BotaAndreiD/Licenta/SimulariLtspice/BlackBox/Electrozi.asc

50HZ: voltage; SINE(0 100m 50)
BaseLineWander: voltage; SINE(0 1 0.02)
CmodelLA: cap; {Cla}
CmodelRA: cap; {Cra}
E1: e; 0.5
E2: e; -0.5
E3: e; -1
EMG: voltage; SINE(0 100m 200)
RmodelLA: res; {Rla}
RmodeRA: res; {Rra}
V1: voltage; PWL file=C:\Users\botaa\Documents\Licenta\AchizitionareSemnal\ekg_signal2.txt
Named nets: 0, VCM, Potential_Corp, LA, RA, RL
