BotaAndreiD/Licenta/SimulariLtspice/BlackBox/Protectie.asc

D1: zener; DI_BZX84C3V6
D2: zener; DI_BZX84C3V6
D3: zener; DI_BZX84C3V6
D4: zener; DI_BZX84C3V6
D5: diode; SMBJ90CA
D6: diode; SMBJ90CA
R1: res; 20k
R2: res; 20k
R3: res; 10k
R4: res; 10k
Named nets: 0, Vcc, ProtectieOut+, ProtectieOut-, ProtectieIn+, ProtectieIn-
.SUBCKT SMBJ90CA     1   2
*       TERMINALS:   T1  T2
Done    1            3   Dtvs
Dtwo    2            3   Dtvs
Rleak   1            2   180meg
.MODEL  Dtvs         D   (IS=1.0e-7 RS=0.4561 N=1.5 IBV=1m BV=105.5 CJO=180p)
.ENDS
