BotaAndreiD/Licenta/SimulariLtspice/BlackBox/PSU.asc

C2: cap; 1u
C3: cap; 1u; Rser=0.5
D1: zener; DI_BZX84C3V6
R1: res; 100k
R2: res; 100k
U1: ADP151-3.3
U2: opamp2; ad8534
Vusb1: voltage; 5
Named nets: 0, Vref, Vcc
