BotaAndreiD/Licenta/SimulariLtspice/BlackBox/RLD.asc

C1: cap; 1n
R7: res; 10Meg
R8: res; 1Meg
U1: opamp2; ad8534
Named nets: Vref, RL, Vcc, 0, VMED
