BotaAndreiD/Licenta/SimulariLtspice/BlackBox/SistemAchizitieECG.asc

R1: res; 10Meg
R2: res; 10Meg
X1: INA
X2: RLD
X3: Electrozi; Rla=51k Rra=100k Cla=47n Cra=47n
X4: FTS
X5: Protectie
X6: FTJ
X7: PSU
X8: NOTCH50
Named nets: VFTJ, Vref, Vcc, VINA, VFTS, VNOTCH
.lib ad8534.cir
.tran 0 35 30
.inc BZX84C3V6.spice.txt
Param. Electrozi
