BotaAndreiD/Licenta/SimulariLtspice/Standard IEC 60601-2-25/EkgIdealFinal.asc

C1: cap; 1000p
C2: cap; 0.1µ
C3: cap; 1µ; Rser=0.5
C4: cap; 1µ
C5: cap; 1µ
C6: cap; 47n
C7: cap; 10µ
C8: cap; 10µ
C9: cap; 10µ
C10: cap; 0.1µ
C11: cap; 0.1µ
C12: cap; 0.22µ
C13: cap; 4700p
C14: cap; 0.1µ
C15: cap; 0.1µ
C16: cap; 47n
C17: cap; 0.1µ
D1: zener; DI_BZX84C3V3
D2: zener; DI_BZX84C3V3
D3: zener; DI_BZX84C3V3
D4: zener; DI_BZX84C3V3
D5: diode; SMBJ90CA
D6: diode; SMBJ90CA
E1: e; 0.5
E2: e; -0.5
E3: e; -1
R1: res; 3Meg
R2: res; 3Meg
R3: res; 1Meg
R4: res; 10Meg
R5: res; 8.66k
R6: res; 100k
R7: res; 100k
R8: res; 316k
R9: res; 20k
R10: res; 158k
R11: res; 620k
R12: res; 1k
R13: res; 10k
R14: res; 31.6k
R15: res; 31.6k
R16: res; 15.4k
R17: res; 274k
R18: res; 3.01k
R19: res; 6.81k
R20: res; 3.92k
R21: res; 23.7k
R22: res; 7.15k
R23: res; 2.87k
R24: res; 20k
R25: res; 10k
R26: res; 9.1k
R27: res; 1k
R28: res; 10k
R29: res; 58k
R30: res; 57k
U1: opamp2; ad8534
U2: ADP151-3.3
U3: opamp2; ad8534
U4: opamp2; ad8534
U5: opamp2; ad8534
U6: opamp2; ad8534
U7: opamp2; ad8534
U8: opamp2; ad8534
U9: opamp2; ad8534
U10: MAX41400
V1: voltage; PWL file=C:\Users\botaa\Documents\Licenta\AchizitionareSemnal\ekg_signal2.txt
V2: voltage; SINE(0 100m 50)
V3: voltage; SINE(0 200m 0.02)
V4: voltage; SINE(0 100m 200)
Vusb1: voltage; 5
Named nets: Vref, Vrld, Vcc, 0, VFts, Vnotch, VCM, Potential_Corp, VINA, Vinp, Vinn, Vekg
.lib ad8534.cir
.tran 0 35 30 uic
.model SW SW(Vt=90 Vh=-5 Ron=0.1 Roff=1G)
.inc BZX84C3V3.spice.txt
.SUBCKT SMBJ90CA     1   2
*       TERMINALS:   T1  T2
Done    1            3   Dtvs
Dtwo    2            3   Dtvs
Rleak   1            2   180meg
.MODEL  Dtvs         D   (IS=1.0e-5 RS=0.4561 N=1.5 IBV=1m BV=105.5 CJO=180p)
.ENDS
