BotaAndreiD/Licenta/SimulariLtspice/Tolerante/Toleranta NOTCH.asc

C4: cap; {wc(100n, 0.05, run)}
C5: cap; {wc(100n, 0.05, run)}
C6: cap; {wc(200n, 0.05, run)}
R6: res; {wc(10k, 0.001, run)}
R7: res; {wc(10k, 0.001, run)}
R8: res; {wc(31.8k, 0.001, run)}
R9: res; {wc(31.8k, 0.001, run)}
R10: res; {wc(15.9k, 0.01, run)}
U3: opamp2; ad8534
U4: opamp2; ad8534
V1: voltage; ""; AC 1
V2: voltage; 3.3
V3: voltage; 1.65
Named nets: 0, Vref, Vcc, Vnotch
.lib ad8534.cir
;tran 0 40 30 uic
.model SW SW(Vt=90 Vh=-5 Ron=0.1 Roff=1G)
.inc BZX84C3V3.spice.txt
.func wc(nominal, tol, index) = nominal*(1 + tol*if(flat(0.5) > 0, 1, -1))
.step param run 1 50 1
.meas AC atenuare_max MIN mag(V(vnotch))
.meas AC freq_centrala WHEN mag(V(vnotch))=atenuare_max
.meas AC atenuare_max MIN mag(V(vnotch))
.meas AC freq_centrala WHEN mag(V(vnotch))=atenuare_max
.ac dec 5000 0.01 300
