BotaAndreiD/Licenta/SimulariLtspice/BlackBox/FTS.asc

C1: cap; 10µ
C2: cap; 10µ
C3: cap; 10µ
R1: res; 319k
R2: res; 159k
R3: res; 637k
R4: res; 9k
R5: res; 1k
U1: opamp2; ad8534
U2: opamp2; ad8534
V1: voltage; 1.65
V2: voltage; 3.3
Named nets: VFTS, VINA, 0, Vref, Vcc
