BotaAndreiD/Licenta/SimulariLtspice/Tolerante/Toleranta FTS.asc

C1: cap; {wc(10u, 0.1, run)}
C2: cap; {wc(10u, 0.1, run)}
C3: cap; 10µ
R1: res; {wc(319k, 0.001, run)}
R2: res; {wc(159k, 0.001, run)}
R3: res; {wc(637k, 0.01, run)}
R4: res; {wc(9k, 0.001, run)}
R5: res; {wc(1k, 0.001, run)}
U1: opamp2; ad8534
U2: opamp2; ad8534
V1: voltage; ""; AC 1
V2: voltage; 3.3
V3: voltage; 1.65
Named nets: Vref, 0, Vcc, vfts
.lib ad8534.cir
;tran 0 40 30 uic
.model SW SW(Vt=90 Vh=-5 Ron=0.1 Roff=1G)
.inc BZX84C3V3.spice.txt
.func wc(nominal, tol, index) = nominal*(1 + tol*if(flat(0.5) > 0, 1, -1))
.step param run 1 50 1
.ac dec 100 0.01 300
.meas AC gain_pass_fts find mag(V(vfts)) AT 10
.meas AC target_3dB_fts param gain_pass_fts/1.414
.meas AC f_cutoff_fts when mag(V(vfts))=target_3dB_fts rise=1
