BotaAndreiD/Licenta/SimulariLtspice/Tolerante/Toleranta GAIN.asc

C1: cap; {wc(1n, 0.1, run)}
C2: cap; 1µ; Rser=0.5
C3: cap; 1µ
C4: cap; 1µ
C5: cap; {wc(100n, 0.1, run)}
C6: cap; {wc(100n, 0.1, run)}
C7: cap; {wc(200n, 0.1, run)}
C8: cap; 100n
C9: cap; {wc(110n, 0.1, run)}
C10: cap; {wc(4.3n, 0.1, run)}
C11: cap; {wc(110n, 0.1, run)}
C12: cap; {wc(110n, 0.1, run)}
C13: cap; 47n
C14: cap; 47n
C15: cap; {wc(10u, 0.1, run)}
C16: cap; {wc(10u, 0.1, run)}
C17: cap; {wc(10u, 0.1, run)}
D1: zener; DI_BZX84C3V3
D2: zener; DI_BZX84C3V3
D3: zener; DI_BZX84C3V3
D4: zener; DI_BZX84C3V3
D5: zener; DI_BZX84C3V3
E1: e; 0.5
E2: e; -0.5
EMG1: voltage; SINE(0 100m 200)
LampaNeon1: sw
R1: res; {wc(10Meg, 0.001, run)}
R2: res; {wc(10Meg, 0.001, run)}
R3: res; {wc(1Meg, 0.001, run)}
R4: res; {wc(20k, 0.001, run)}
R5: res; {wc(20k, 0.001, run)}
R6: res; 100k
R7: res; 100k
R8: res; {wc(10k, 0.001, run)}
R9: res; {wc(10k, 0.001, run)}
R10: res; {wc(31.8k, 0.001, run)}
R11: res; {wc(31.8k, 0.001, run)}
R12: res; {wc(15.9k, 0.001, run)}
R13: res; {wc(10k, 0.001, run)}
R14: res; {wc(10k, 0.001, run)}
R15: res; {wc(8.59k, 0.001, run)}
R16: res; {wc(277k, 0.01, run)}
R17: res; {wc(2.99k, 0.001, run)}
R18: res; {wc(6.81k, 0.001, run)}
R19: res; {wc(3.94k, 0.001, run)}
R20: res; {wc(23.6k, 0.001, run)}
R21: res; {wc(7.1k, 0.001, run)}
R22: res; {wc(2.87k, 0.001, run)}
R23: res; 51k
R24: res; 100k
R25: res; {wc(319k, 0.001, run)}
R26: res; {wc(159k, 0.001, run)}
R27: res; {wc(637k, 0.01, run)}
R28: res; {wc(9k, 0.001, run)}
R29: res; {wc(1k, 0.001, run)}
R30: res; {wc(10Meg, 0.001, run)}
S1: sw
U1: opamp2; ad8534
U2: ADP151-3.3
U3: opamp2; ad8534
U4: opamp2; ad8534
U5: opamp2; ad8534
U6: MAX41400
U7: opamp2; ad8534
U8: opamp2; ad8534
U9: opamp2; ad8534
U10: opamp2; ad8534
V1: voltage; PWL file=C:\Users\botaa\Documents\Licenta\Licenta\AchizitionareSemnal\ekg_signal2.txt; AC 1
V2: voltage; SINE(0 100m 50)
V3: voltage; SINE(0 100m 0.01)
Vusb1: voltage; 5
Named nets: Vref, Vrld, Vcc, 0, Vnotch, VCM, VINA, Vinp, Vinn, Vekg, VFts
.lib ad8534.cir
.model SW SW(Vt=90 Vh=-5 Ron=0.1 Roff=1G)
.inc BZX84C3V3.spice.txt
.func wc(nominal, tol, index) = nominal*(1 + tol*if(flat(0.5) > 0, 1, -1))
.step param run 1 5 1
.ac dec 100 0.1 1000
.meas AC gain_total_vfind find mag(V(Vout)) AT 10
.meas AC gain_max_db MAX mag(V(Vout))
