BotaAndreiD/Licenta/SimulariLtspice/Tolerante/Tolerante FTJ.asc

C1: cap; {wc(110n, 0.1, run)}
C2: cap; {wc(4.3n, 0.1, run)}
C3: cap; {wc(110n, 0.1, run)}
C4: cap; {wc(110n, 0.1, run)}
R1: res; {wc(8.59k, 0.001, run)}
R2: res; {wc(277k, 0.01, run)}
R3: res; {wc(2.99k, 0.001, run)}
R4: res; {wc(6.81k, 0.001, run)}
R5: res; {wc(23.6k, 0.001, run)}
R6: res; {wc(7.1k, 0.001, run)}
R7: res; {wc(2.87k, 0.001, run)}
R8: res; {wc(3.94k, 0.001, run)}
U1: opamp2; ad8534
U2: opamp2; ad8534
V1: voltage; 3.3
V2: voltage; 1.65
V3: voltage; ""; AC 1
Named nets: 0, Vref, Vcc, Vekg
.lib ad8534.cir
;tran 0 40 30 uic
.model SW SW(Vt=90 Vh=-5 Ron=0.1 Roff=1G)
.inc BZX84C3V3.spice.txt
.func wc(nominal, tol, index) = nominal*(1 + tol*if(flat(0.5) > 0, 1, -1))
.step param run 1 50 1
.ac dec 100 0.01 300
.meas AC gain_pass find mag(V(vekg)) AT 10
.meas AC target_3dB param gain_pass/1.414
.meas AC f_cutoff when mag(V(vekg))=target_3dB fall=1
