BotaAndreiD/Licenta/SimulariLtspice/Standard IEC 60601-2-25/Draft1.asc

C1: cap; 82n
C2: cap; 82n
R1: res; 137k
R2: res
U1: AD8032
V1: voltage; 2.7
Named nets: 0, Vcc
