BotaAndreiD/Licenta/SimulariLtspice/Standard IEC 60601-2-25/CMRR89dB.asc

C1: cap; 1n
C2: cap; 1µ; Rser=0.5
C3: cap; 1µ
C4: cap; 1µ
C5: cap; 10µ
C6: cap; 10µ
C7: cap; 10µ
C8: cap; 10µ
C9: cap; 100n
C10: cap; 100n
C11: cap; 200n
C12: cap; 390n
C13: cap; 16n
C14: cap; 390n
C15: cap; 390n
C16: cap; 100n
C17: cap; 10µ
D1: zener; DI_BZX84C3V3
LampaNeon1: sw
R1: res; 4.7Meg
R2: res; 4.7Meg
R3: res; 1Meg
R4: res; 20k
R5: res; 20k
R6: res; 100k
R7: res; 100k
R8: res; 41.1k
R9: res; 63.5k
R10: res; 81.2k
R11: res; 25.6k
R12: res; 1k
R13: res; 10k
R14: res; 31.8k
R15: res; 31.8k
R16: res; 15.9k
R17: res; 9.1k
R18: res; 279k
R19: res; 2.99k
R20: res; 6.81k
R21: res; 4.16k
R22: res; 25k
R23: res; 7.1k
R24: res; 2.87k
R25: res; 6.06k
R26: res; 3.92k
R27: res; 7.29k
R28: res; 2.49k
R29: res; 10k
R30: res; 10k
R31: res; 10Meg
S1: sw
U1: opamp2; ad8534
U2: ADP151-3.3
U3: opamp2; ad8534
U4: opamp2; ad8534
U5: opamp2; ad8534
U6: opamp2; ad8534
U7: opamp2; ad8534
U8: opamp2; ad8534
U9: opamp2; ad8534
U10: BAV99
U11: BAV99
U12: BAV99
U13: BAV99
U14: MAX41400
U15: opamp2; ad8534
V3: voltage; ""; AC 1
Vusb1: voltage; 5
Named nets: Vref, Vrld, Vcc, 0, VFts, Vnotch, VCM, Vekg, VINA, Vinp, Vinn
.lib ad8534.cir
.tran 0 40 30 uic
.model SW SW(Vt=90 Vh=-5 Ron=0.1 Roff=1G)
.inc BZX84C3V3.spice.txt
.ac dec 100 0.5 1k
